build-aweigh/build-aweigh/Design/3D Printed/final/9.stl

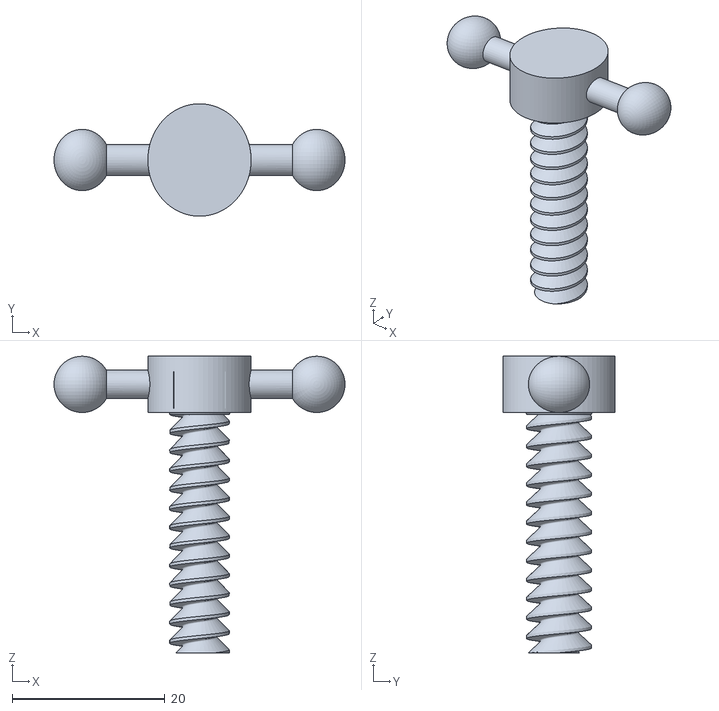
[picture p22: CAD file, 2019-01-18]
Design/3D Printed/final/9.stl
38.1 x 14.7 x 38.9
