build-aweigh/build-aweigh/Design/3D Printed/final/11.stl

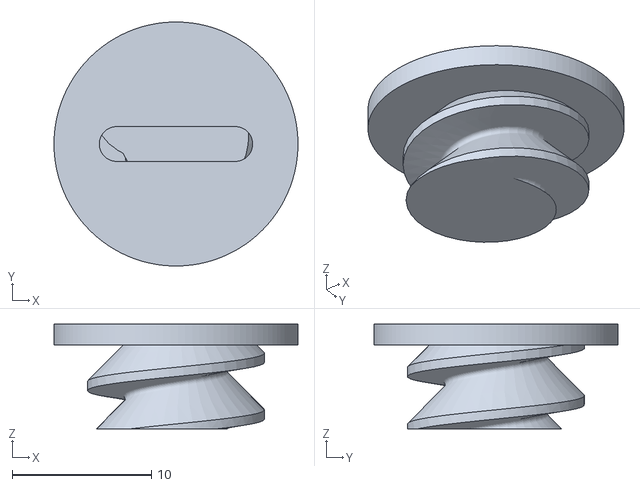
[picture p23: CAD file, 2019-01-18]
Design/3D Printed/final/11.stl
17.5 x 17.5 x 7.50
